goran-mahovlic/megaphone-modular/modules/lcd-panel/RTW0024A.stp

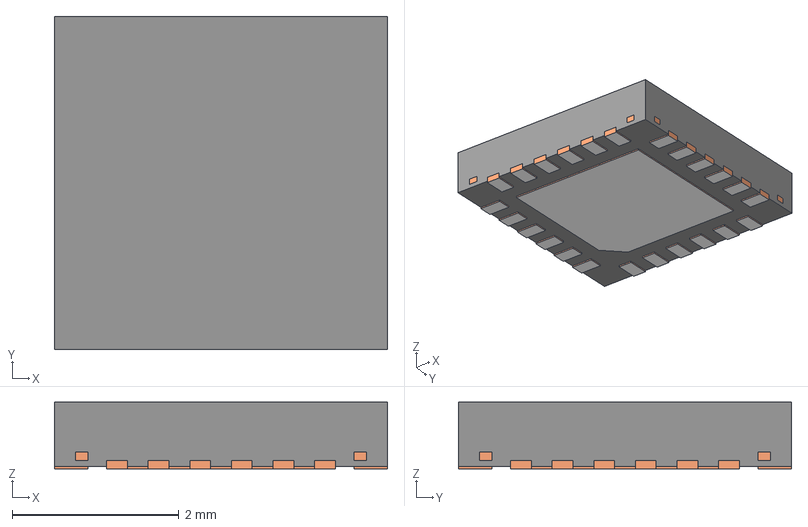
[picture p16: CAD file, 2025-04-25]
modules/lcd-panel/RTW0024A.stp
4.00 x 4.00 x 0.8 mm
BODY-QFN
FRAME-RTW0024A
PIN1-ID
