goran-mahovlic/megaphone-modular/modules/input-power-selector/footprints/PowerPAK_8x8L_BWL-2_VIS.step

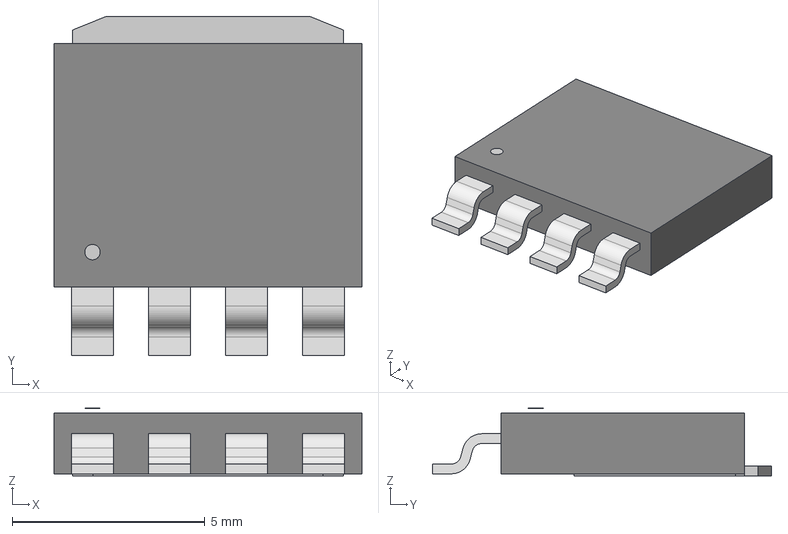
[picture p17: CAD file, 2025-03-05]
modules/input-power-selector/footprints/PowerPAK_8x8L_BWL-2_VIS.step
8.00 x 8.81 x 1.75 mm
