goran-mahovlic/megaphone-modular/modules/input-power-selector/footprints/IPF067N20NM6ATMA1.stp

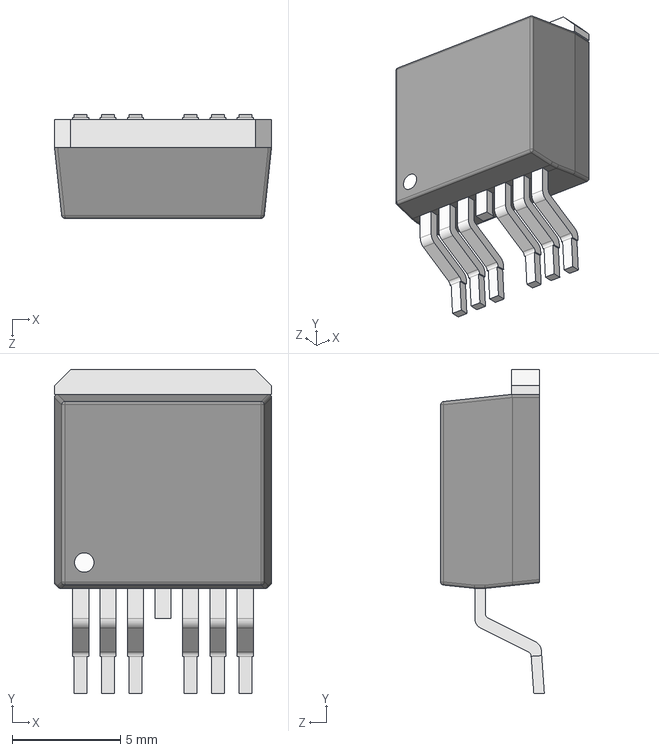
[picture p18: CAD file, 2025-03-05]
modules/input-power-selector/footprints/IPF067N20NM6ATMA1.stp
10.1 x 15.0 x 4.80 mm
