goran-mahovlic/megaphone-modular/modules/input-power-selector/footprints/TSM4800N15CX6RFG.STEP

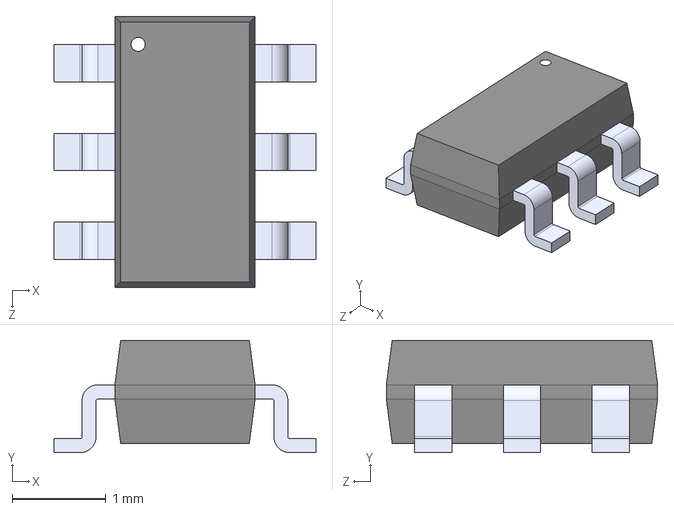
[picture p19: CAD file, 2025-03-05]
modules/input-power-selector/footprints/TSM4800N15CX6RFG.STEP
2.80 x 1.20 x 2.90 mm
