goran-mahovlic/megaphone-modular/modules/audio-jack/audio-jack.kicad_pcb

## KiCad design modules/audio-jack/audio-jack.kicad_pcb (2025-04-30)

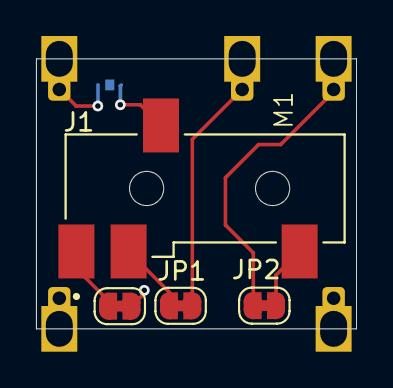
[picture p38: board audio-jack.kicad_pcb from above]

Board: 2 copper layers, 17.8 x 15.0 mm, 6 parts (1 on the bottom side), 8 nets.

Parts:
J1: SJ-43514-SMT-TR; CUI_SJ-43514-SMT-TR
JP1, JP2, JP3, JP4: Jumper_2_Bridged; SolderJumper-2_P1.3mm_Bridged_RoundedPad1.0x1.5mm
M1: MegaCastle2x7-Module-I15.0x13.0-M8314-SPAREPAD

Connections:
GND: JP3.2 (B), M1.7 (GND)
LEFT: JP4.1 (A), M1.8
MIC: JP1.2 (B), M1.12
unnamed: J1.4, JP1.1 (A)
unnamed: J1.2, JP2.2 (B)
unnamed: J1.1, JP3.1 (A)
unnamed: J1.3, JP4.2 (B)
RIGHT: JP2.1 (A), M1.14
